svediNL/Grow/arduino/arduino_main/grow.h

#ifndef GROW_H
#define GROW_H

#include <Arduino.h>
#include "sensors.h" 
#include "actuators.h"
#include "comms.h"
#include "timekeeping.h"

#include <Wire.h>
#include <Adafruit_AM2315.h>

// !!! WARNING - DO NOT USE PINS 9 & 10 FOR PWM, AS THIS WILL FUCK UP THE TIMER !!!


// ENABLE/DISABLE DEVICES

// PWM DIMMABLE LAMP CONFIGURATION
const int     NR_LAMP                     = 1;                // NUMBER OF LAMPS TO BE CONFIGURED
const int     LAMP_RGBW_PIN [NR_LAMP][4]  = { {-1,-1,-1,8} };  // 2D ARRAY OF PWM PINS
const String  LAMP_NAME     [NR_LAMP]     = {"RGBW LED PWM output"};

// CONFIGURE DOOR SWITCH TO DIM LIGHT WHEN DOOR OPENS
const bool  ENABLE_FRIDGE_DOOR  = true;   // light dims when door opens
const int   DOOR_SWITCH_PIN     = 25;     // DIGITAL OUTPUT PIN          

// THERMOCOUPLE CONFIGURATION
const int     NR_TC             = 2;                  // NUMBER OF THERMOCOUPLE TO BE CONFIGURED
const int     TC_PIN  [NR_TC]   = {A1, A2};           // ARRAY OF ANALOG INPUT PINS
const String  TC_NAME [NR_TC]   = {"thermocouple 0", "thermocouple 1"};

// RELAY CONFIGURATION
const int NR_RELAY                  = 8;                                  // NUMBER OF RELAYS TO BE CONFIGURED
const int RELAY_PIN     [NR_RELAY]  = {24, 26, 28, 30, 32, 34, 36, 38};   // ARRAY OF DIGITAL OUTPUT PINS
const String RELAY_NAME [NR_RELAY]  = {"12V Enable", "Valve 0", "Valve 2", "Valve 3", "Valve 4", "Valve 5", "Fans Lamp", "NC"};

// MOISTURE SENSOR CONFIGURATION
const int     NR_MOISTURE                        = 1;     // number of MOISTURE SENSORs to be configured
const int     MOISTURE_INPUT_PIN  [NR_MOISTURE]  = {A0};  // array of ANALOG INPUT PINs
const int     MOISTURE_POWER_PIN  [NR_MOISTURE]  = {22};  // array of DIGITAL OUTPUT PINs
const String  MOISTURE_NAME       [NR_MOISTURE]  = {"water sensor - analog input"};
const String  MOISTURE_POWER_NAME [NR_MOISTURE]  = {"water sensor - power enable"};

// PUMP H-BRIDGE CONFIGURATION
const int     NR_PUMP                 = 1;    // NUMBER OF PUMPS TO CONFIGURE
const int     PUMP_DIR_PIN [NR_PUMP]  = {7};  // ARRAY OF PWM PINS
const int     PUMP_PWM_PIN [NR_PUMP]  = {6};  // ARRAY OF PWM PINS
const String  PUMP_NAME    [NR_PUMP]  = {"pump on H-Bridge board"};

// ON/OFF LEVEL SENSOR (FLOAT SWITCH)
const bool  ENABLE_PUMP_INTERLOCK_SWITCH  		      = true;   	// SETUP HAS FLOAT SWITCH
const int   NR_FLOAT_SWITCH               		      = 1;			// NUMBER OF FLOAT SWITCHES TO BE CONFIGURED
const int   FLOAT_SWITCH_PIN       [NR_FLOAT_SWITCH]  = {23};		// PIN NR OF FLOAT SWITCH(es)
const int   PUMP_INTERLOCK_LINKING [NR_FLOAT_SWITCH]  = {0};    	// LINK FLOAT SWITCH TO PUMP(s)
//const int   FLOAT_VALVE_INTERLOCK_LINKING  		= {0};    	// LINK FLOAT SWITCH TO VALVE(s)

enum Device { NONE, PUMP, LAMP };

class Grow
{
  public:
    Comms serialMsg;

    RGBWLed lamp[NR_LAMP];                                // INSTANCE OF RGBW PWM LIGHT OUTPUT
    
    DigitalInput doorSensor;                              // INSTANCE OF DOOR SENSOR FOR DIMMING OF LIGHT
    
    AnalogSensor thermocouple[NR_TC]; // INSTANCE THERMOCOUPLE ANALOG SENSOR (VOLTAGE READOUT)
    
    DigitalOutput relayboard[NR_RELAY];                                 // INSTANCE OF DIGITAL OUTUT FOR RELAY BOARD (OR COMBINATION THEREOF) [implemented on standard solution: 5V -> OPTOCOUPLER -> RELAY]
    
    AnalogSensor  moisture[NR_MOISTURE];                // INSTANCE OF MOISTURE SENSOR ANALOG SENSOR
    DigitalOutput moisturePower[NR_MOISTURE];           // INSTANCE OF POWER ENABLE TO MOISTURE SENSOR
    MotorDriver pump[NR_PUMP];             // INSTANCE OF PUMP H-BRIDGE MOTOR DRIVER
    DigitalInput vlotter[NR_FLOAT_SWITCH];         // INSTANCE OF LOAT SWITCH FOR PUMP INTERLOCKING
    TimeKeeper masterClock;

    Adafruit_AM2315 am2315; // I2C HUMIDITY+TEMPERATURE SENSOR AM2315
    
    void init();
    void doStuff();		// DO OPERATIONS/CHECKS/WHATEREVER IN LOOP()

    //int counter = 0;
    bool bNewMessage = false;
    String serialString;

  private:
    float rntc, vin, vm;
    float rc[NR_TC];
    float Tn, Rn, coeffB, temp;

    float i2c_temp, i2c_hum;

    byte 	schedule_index=0;
	  byte 	scheduled_timer[NR_SUBTIMER];
	  Device 	scheduled_device[NR_SUBTIMER];
	  byte 	scheduled_device_id[NR_SUBTIMER];
	  int 	scheduled_value[NR_SUBTIMER];

  	bool x;
    void fridge_door();

    bool overrule_pump_interlock[NR_PUMP];
    void check_pump_interlock();

    bool push_to_schedule(Device myDevice, byte deviceID, int timePar, int value); //returns false when failed
	  void scheduler();

    void doCommand();	// DO COMMAND FROM SERIAL COMMS
    void printHelp();
};

#endif
